tomojitakasu/SCH63T_MINI_EVK/HW/image1684.jpg

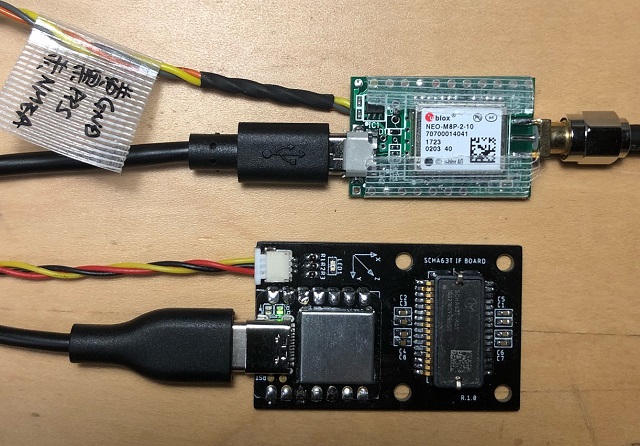
HW/image1684.jpg
